schwarzschildkugelblitz/The_Hive/PCB/PCB_v2/pcb_flip.png

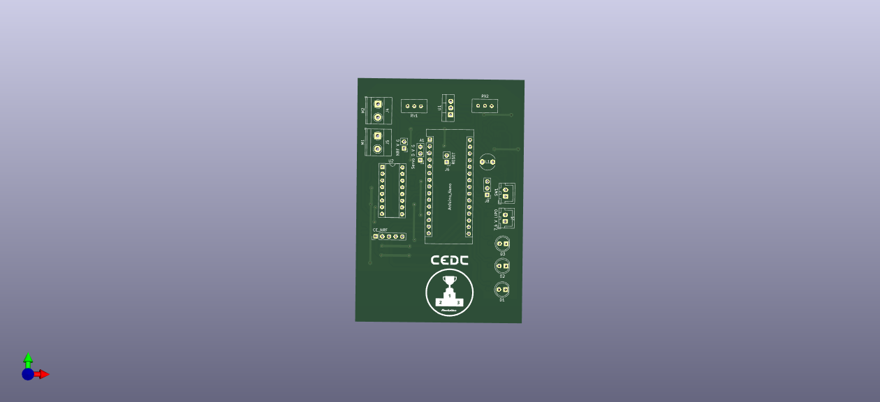
PCB/PCB_v2/pcb_flip.png
