schwarzschildkugelblitz/The_Hive/central_tracking/markers/0.jpg

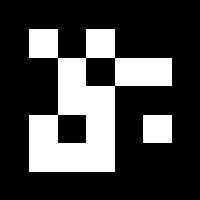
central_tracking/markers/0.jpg
