schwarzschildkugelblitz/The_Hive/central_tracking/markers/1.jpg

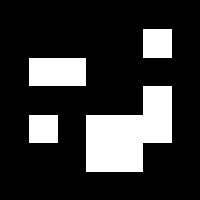
central_tracking/markers/1.jpg
