schwarzschildkugelblitz/The_Hive/central_tracking/markers/2.jpg

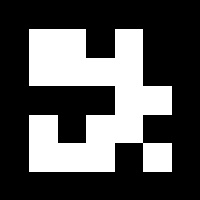
central_tracking/markers/2.jpg
