schwarzschildkugelblitz/The_Hive/central_tracking/markers/3.jpg

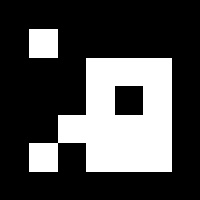
central_tracking/markers/3.jpg
