schwarzschildkugelblitz/The_Hive/central_tracking/markers/4.jpg

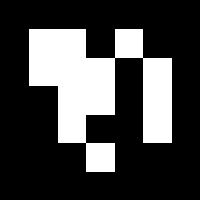
central_tracking/markers/4.jpg
