schwarzschildkugelblitz/The_Hive/central_tracking/markers/5.jpg

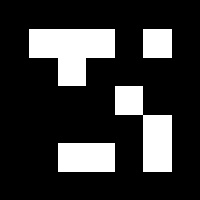
central_tracking/markers/5.jpg
