schwarzschildkugelblitz/The_Hive/central_tracking/markers/6.jpg

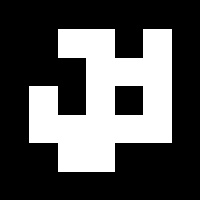
central_tracking/markers/6.jpg
