schwarzschildkugelblitz/The_Hive/central_tracking/markers/7.jpg

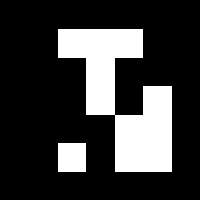
central_tracking/markers/7.jpg
