schwarzschildkugelblitz/The_Hive/central_tracking/markers/8.jpg

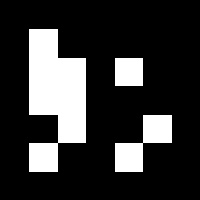
central_tracking/markers/8.jpg
