schwarzschildkugelblitz/The_Hive/central_tracking/markers/9.jpg

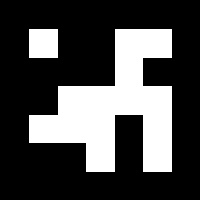
central_tracking/markers/9.jpg
