schwarzschildkugelblitz/The_Hive/central_tracking/markers/10.jpg

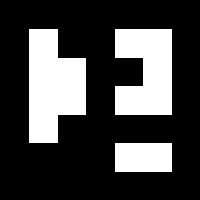
central_tracking/markers/10.jpg
