schwarzschildkugelblitz/The_Hive/central_tracking/markers/11.jpg

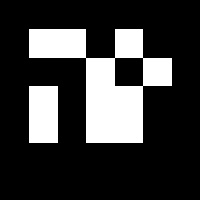
central_tracking/markers/11.jpg
