schwarzschildkugelblitz/The_Hive/central_tracking/markers/12.jpg

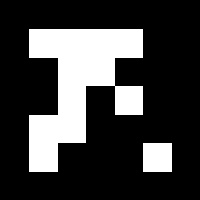
central_tracking/markers/12.jpg
