schwarzschildkugelblitz/The_Hive/central_tracking/markers/13.jpg

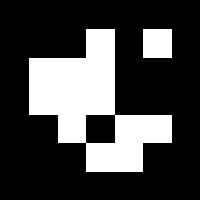
central_tracking/markers/13.jpg
