schwarzschildkugelblitz/The_Hive/central_tracking/markers/14.jpg

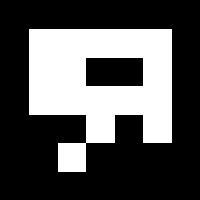
central_tracking/markers/14.jpg
