schwarzschildkugelblitz/The_Hive/central_tracking/markers/15.jpg

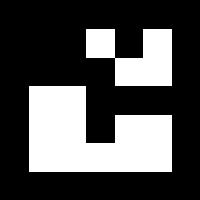
central_tracking/markers/15.jpg
