schwarzschildkugelblitz/The_Hive/central_tracking/markers/16.jpg

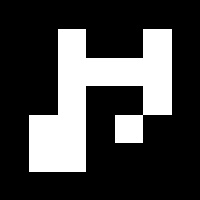
central_tracking/markers/16.jpg
