schwarzschildkugelblitz/The_Hive/central_tracking/markers/17.jpg

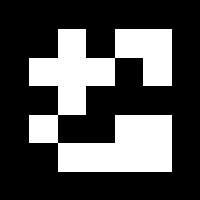
central_tracking/markers/17.jpg
