schwarzschildkugelblitz/The_Hive/central_tracking/markers/18.jpg

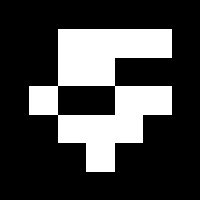
central_tracking/markers/18.jpg
