schwarzschildkugelblitz/The_Hive/central_tracking/markers/19.jpg

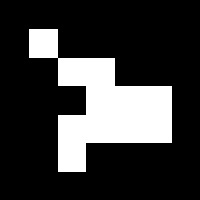
central_tracking/markers/19.jpg
