schwarzschildkugelblitz/The_Hive/worker_bee/transmission/transmission.ino

// TX <<<<<<<<<<<<<<<<<<<<<<<<<<<<<<<<<<<<
// flow : s1 -> recv -> parsedData -> address , angle + sign , distance + sign -> PID -> V 
//-> signed speed -> unsigned speed + sign bit - > TX

#include <SPI.h>
#include <RH_NRF24.h>

#define stopButton  2

// 1st 8 bit number -> 2 bit address + 6 bit modes
// 2nd 8 bit number => 1 sign bit , 4 bit base speed , 3 empty bits
RH_NRF24 nrf24(9, 10);
uint8_t data[2];
int x =0;
uint8_t parsedData[2];
void stopAll() // modify the data to be sent
{

while (digitalRead(2)==HIGH)
{
  for(x = 0; x < 4;x++)
  {
 
  parsedData[0] = x+4*58; // XXXX(A1)(A0) & 000011 + 1110 1000 = 1110 10(A1)(A0) : 58 is the stop code
  nrf24.send(parsedData, sizeof(parsedData)); // send data
  nrf24.waitPacketSent();
   parsedData[0] = x+4*58; // XXXX(A1)(A0) & 000011 + 1110 1000 = 1110 10(A1)(A0) : 58 is the stop code
  nrf24.send(parsedData, sizeof(parsedData)); // send data
  nrf24.waitPacketSent();
  }
}
}


void setup()
{
  Serial.begin(115200);
  pinMode(stopButton, INPUT_PULLUP); // already refrenced to +5v / HIGH via pullup
  attachInterrupt(digitalPinToInterrupt(stopButton), stopAll, RISING);
  if (!nrf24.init());
//    Serial.println("init failed");
  if (!nrf24.setChannel(1));
//    Serial.println("setChannel failed");
  if (!nrf24.setRF(RH_NRF24::DataRate2Mbps, RH_NRF24::TransmitPower0dBm));
//    Serial.println("setRF failed");    

}

// float timi=millis(),timf,D,x,V=0,filter_state=0,integrator_state=0; // implemented in py
// float Kp=0.00025,Kd=0.0155,Ki=0.000085,N=34;// tuned values
// int add,speed,sign,speed2=0,misc=0;
 int theta,dist,i,k; // index vars


void loop()
{
  // 0 1 2 3 -> angle +ve , distance +ve , 4 5  
  parsedData[0] =0;// do not change default state 
  parsedData[1] =0;
  String s1;
  char recv[10];//max
  
  while (!Serial.available());  // w8 until serial monitor sends out a response
  
  s1 = Serial.readStringUntil('\n');
  s1.toCharArray(recv,sizeof(recv)); 
  
  // process the char array
  i=0;
  k=0; // index vars
  // 1 2 3 
  
  while(recv[i]!='\0')
  {
    if(recv[i] == ' ')
      k++; // skip to next pack
    else
      parsedData[k]=parsedData[k]*10+recv[i]-48; // add the new digit
   
    i++;
  }
   
  nrf24.send(parsedData, sizeof(parsedData)); // send data
  nrf24.waitPacketSent();
  //delay(22); // maintain sync
}
