schwarzschildkugelblitz/The_Hive/central_tracking/fetch_job.py

jobs = [

["FKMP0001", "1", "Ahmedabad"],
    ["FKMP0002", "1", "Pune"],  # Burner
    
    
    
    ["FKMP0002", "1", "Pune"],  # Burner
    ["FKMP0002", "1", "Pune"],  # Burner

    ["FKMP0002", "1", "Pune"],
    ["FKMP0003", "2", "Ahmedabad"],
    ["FKMP0004", "2", "Bengaluru"],
    ["FKMP0005", "2", "Kolkata"],
    ["FKMP0006", "1", "Mumbai"],
    ["FKMP0007", "2", "Delhi"],
    ["FKMP0008", "2", "Delhi"],
    ["FKMP0009", "2", "Bengaluru"],
    ["FKMP0010", "2", "Ahmedabad"],
    ["FKMP0011", "1", "Delhi"],
    ["FKMP0012", "2", "Chennai"],
    ["FKMP0013", "1", "Jaipur"],
    ["FKMP0014", "1", "Mumbai"],
    ["FKMP0015", "2", "Hyderabad"],
    ["FKMP0016", "1", "Kolkata"],
    ["FKMP0017", "1", "Bengaluru"],
    ["FKMP0018", "2", "Chennai"],
    ["FKMP0019", "2", "Ahmedabad"],
    ["FKMP0020", "1", "Kolkata"],
    ["FKMP0021", "1", "Delhi"],
    ["FKMP0022", "1", "Jaipur"],
    ["FKMP0023", "2", "Hyderabad"],
    ["FKMP0024", "1", "Delhi"],
    ["FKMP0025", "2", "Bengaluru"],
    ["FKMP0026", "2", "Bengaluru"],
    ["FKMP0027", "2", "Ahmedabad"],
    ["FKMP0028", "1", "Chennai"],
    ["FKMP0029", "2", "Bengaluru"],
    ["FKMP0030", "2", "Bengaluru"],
    ["FKMP0031", "2", "Hyderabad"],
    ["FKMP0032", "2", "Chennai"],
    ["FKMP0033", "2", "Mumbai"],
    ["FKMP0034", "2", "Delhi"],
    ["FKMP0035", "1", "Hyderabad"],
    ["FKMP0036", "1", "Delhi"],
    ["FKMP0037", "2", "Jaipur"],
    ["FKMP0038", "2", "Mumbai"],
    ["FKMP0039", "1", "Kolkata"],
    ["FKMP0040", "1", "Kolkata"],
    ["FKMP0041", "1", "Kolkata"],
    ["FKMP0042", "2", "Hyderabad"],
    ["FKMP0043", "1", "Delhi"],
    ["FKMP0044", "2", "Chennai"],
    ["FKMP0045", "2", "Delhi"],
    ["FKMP0046", "2", "Ahmedabad"],
    ["FKMP0047", "1", "Hyderabad"],
    ["FKMP0048", "1", "Bengaluru"],
    ["FKMP0049", "2", "Ahmedabad"],
    ["FKMP0050", "1", "Jaipur"],
    ["FKMP0051", "1", "Delhi"],
    ["FKMP0052", "2", "Mumbai"],
    ["FKMP0053", "1", "Ahmedabad"],
    ["FKMP0054", "1", "Delhi"],
    ["FKMP0055", "2", "Kolkata"],
    ["FKMP0056", "2", "Ahmedabad"]
]


def job_generator():
    for job in jobs:
        yield job
